OLIMEX/OLIMEXINO-STM32F3/HARDWARE/OLIMEXINO-STM32F3-revision-B/3d/L-CD43_shielded.STEP

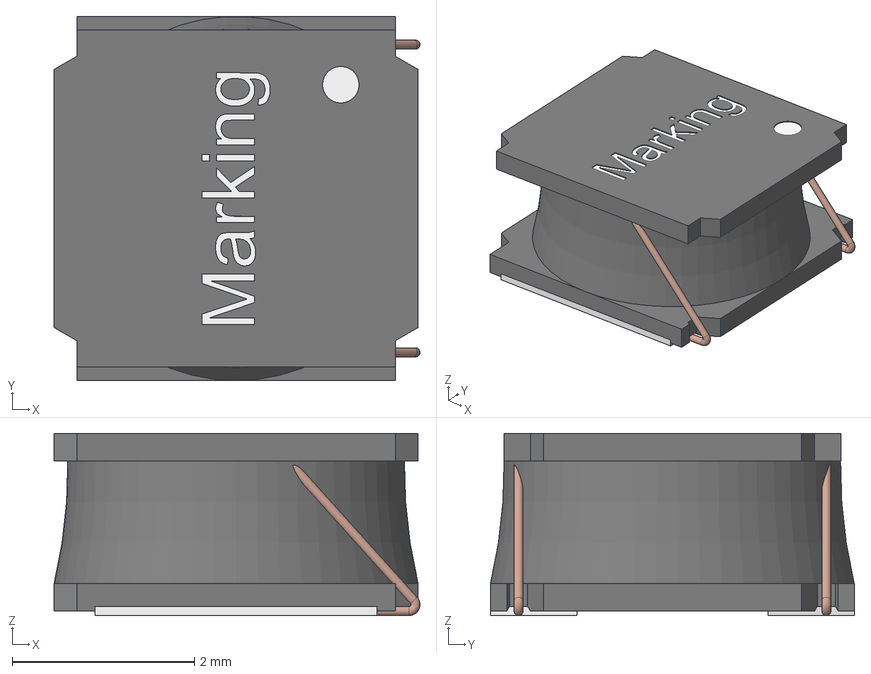
[picture p28: CAD file, 2022-09-20, an earlier design]
HARDWARE/OLIMEXINO-STM32F3-revision-B/3d/L-CD43_shielded.STEP
4.02 x 4.00 x 2.00 mm
housing
contact x 2
Glue
Wire x 2
