OLIMEX/OLIMEXINO-STM32F3/HARDWARE/OLIMEXINO-STM32F3-revision-B/3d/pj-102ah.stp

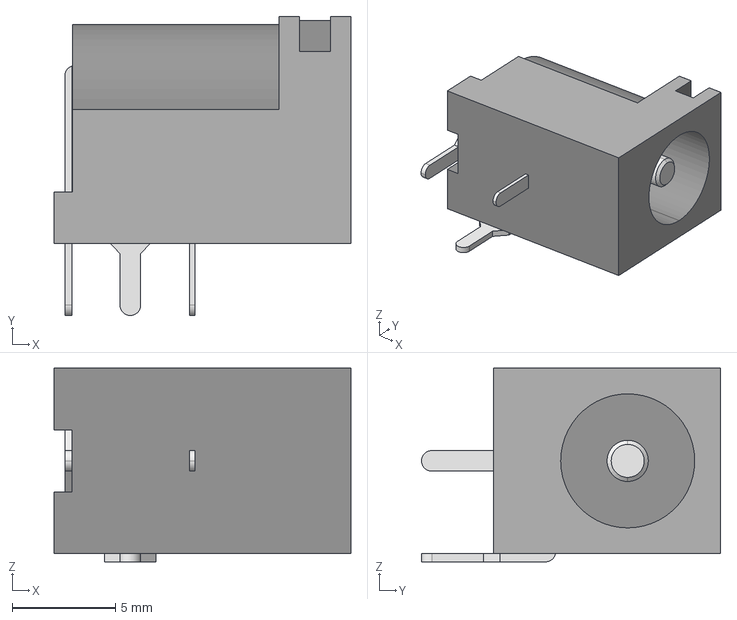
[picture p29: CAD file, 2022-09-20, an earlier design]
HARDWARE/OLIMEXINO-STM32F3-revision-B/3d/pj-102ah.stp
14.4 x 14.5 x 9.40 mm
