OLIMEX/OLIMEXINO-STM32F3/HARDWARE/OLIMEXINO-STM32F3-revision-B/3d/Pin_Header_Straight_2x05_1.27mm.step

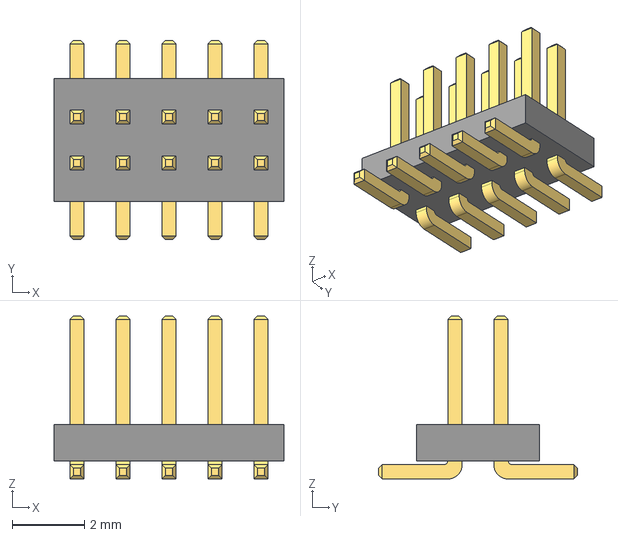
[picture p30: CAD file, 2020-07-31, an earlier design]
HARDWARE/OLIMEXINO-STM32F3-revision-B/3d/Pin_Header_Straight_2x05_1.27mm.step
6.35 x 5.50 x 4.50 mm
