OLIMEX/OLIMEXINO-STM32F3/SOFTWARE/Olimexino-STM32F3_GPIO/Olimexino-STM32F3_GPIO.ino

/*
 * Toggle LED1 (Green) with interval ~1 sec
 * LED2 (Yellow) changes state depending on the state of the button
 */

int Time, PrevTime=0;

void setup()
{
  pinMode (USER_BTN, INPUT);
  pinMode (PA1, OUTPUT);
  pinMode (LED2, OUTPUT);
}

void loop()
{
  Time = millis ();
  if (Time >= PrevTime + 1000)
  {
    PrevTime = Time;
    digitalWrite (PA1, !digitalRead(PA1));
  }
  digitalWrite (LED2, digitalRead(USER_BTN));
}
